piyush-g0enka/two-wheeled-self_balancing_bot/Two wheeled self balancing bot/resources/Balance_Bot_resources.pdf

## RESOURCES

1. Filter (https://bayesianadventures.wordpress.com/2013/10/20/gyroscopes-accelerometers-and-the-complementary-filter/)
2. Complementary filter with the MPU6050 (https://forum.arduino.cc/index.php?topic=215997.0)
3. Brokking.net - Your Arduino Balancing Robot (YABR) - Home. (http://www.brokking.net/yabr_main.html)
4. Self Balancing Robot using LQR (https://forum.arduino.cc/index.php?topic=435836.0)
5. How Balance Bots work — Rover documentation (https://ardupilot.org/rover/docs/balance_bot-working.html)
6. Self Balancing Arduino Robot_PID : 6 Steps (with Pictures) - Instructables (https://www.instructables.com/id/Two-Wheel-Balanced-RobotPID/)
7. Stages of development of the balancing robot (http://spin7ion.ru/ru/blog/balancerBuildSteps)
8. Arduino script for MPU-6050 auto-calibration | (https://42bots.com/tutorials/arduino-script-for-mpu-6050-auto-calibration/)
9. I2Cdevlib: MPU6050 Class Reference (https://www.i2cdevlib.com/docs/html/class_m_p_u6050.html)
10. DIY Self Balancing Robot using Arduino (https://circuitdigest.com/microcontroller-projects/arduino-based-self-balancing-robot)
11. How to Build a Self-Balancing Autonomous Arduino Bot | Make: (https://makezine.com/projects/arduroller-self-balancing-robot/)
12. Self-Balancing Two Wheeled Robot (https://ideaexchange.uakron.edu/cgi/viewcontent.cgi?article=1110&context=honors_research_projects)
13. Interfacing MPU-6050 GY-521 Accelerometer Gyrometer with Arduino Uno (https://electrosome.com/interfacing-mpu-6050-gy-521-arduino-uno/)
